will127534/RaspberryPiAtomicNixieClock/PCB/NixieAtomicClock.kicad_sch

## KiCad design PCB/NixieAtomicClock.kicad_sch (2021-09-04)

Schematic: NixieAtomicClock.kicad_sch

Parts:
C1, C3, C7, C12, C33, C56, C66, C89: 100nF; C_0201_0603Metric
C4, C10, C85, C97, C102: CGA5L1X7R1H106K160AC; C_1206_3216Metric
C5: 390pF; C_0201_0603Metric
C6, C8, C9: 680pF; C_0201_0603Metric
C13, C16, C70: 100nF; C_0603_1608Metric
C14, C19, C21, C23, C28, C29, C30, C31, C32, C38, C39, C41, C46, C50, C55, C57, C62, C67, C68, C71, C78, C80, C81, C82, C83, C84, C86, C87, C99: 100nF; C_0402_1005Metric
C17, C27, C47, C48, C100: 1uF; C_0201_0603Metric
C18, C101: 47uF; C_1206_3216Metric
C20, C22: 4.7uF; C_0402_1005Metric
C24, C25, C49, C75, C76, C77, C79: 10uF; C_0402_1005Metric
C26, C43, C51, C53, C61, C74, C98, C104, C105: 1uF; C_0402_1005Metric
C34: 15pF; C_0402_1005Metric
C36, C73: ACH32C-104-T001
C37, C42, C44, C69, C90: GRM188R60J476ME15J; C_0603_1608Metric
C40: CGA5L1X7R1H106K160AC; C_0805_2012Metric
C45: 47uF; C_0805_2012Metric
C52: 10uF; C_0805_2012Metric
C54: EMZR100ARA102MHA0G; CP_Elec_8x10
C58, C59, C60, C63: 56pF; C_0402_1005Metric
C72, C91: 10uF; C_0603_1608Metric
C88, C92, C93, C94: 1uF; C_0603_1608Metric
D1, D2, D3, D4, D5, D6, D7, D8, D10, D12, D14, D17, D18, D19, D20: SMD-LED-CLEAR-BLUE_0603_; LED-0603; MPN 19-217-BHC-ZL1M2RY-3T
D9, D11, D13, D15, D16: D_TVS; D_0402_1005Metric
FAN1, FAN2: M06SMD-1MM; 1X06-1MM
FL2: DLW5ATH500MQ2L; FIL_DLW5ATH500MQ2L; PARTREV N/A
H1, H2, H5, H6, H7, H8: MOUNT-HOLE3.2; 3,2
J1, J2: M06SMD-1MM; 1X06-1MM
J3: M024UCON-15767; JST-2-SMD-VERT
J4, J5: CONN-POWER-JACK-2.1MM_DC-005_; DCJ3P-11.6X9.6X7.0MM; MPN DC-005
J6: 1-1734248-5; TE_1-1734248-5
J7: 47219-2001; MOLEX_47219-2001
J8: QWIIC_CONNECTORJS-1MM; 1X04_1MM_RA
J9, J10, J11: Conn_Coaxial; U.FL_Hirose_U.FL-R-SMT-1_Vertical
J12: USB_C_Receptacle_USB2.0; USB_C_Receptacle_XKB_U262-16XN-4BVC11
J13, J14, J15, J16: Conn_Coaxial; SMA_Samtec_SMA-J-P-X-ST-EM1_EdgeMount
L1, L5: 27nH; L_0402_1005Metric
L2, L3, L4: 1uH; L_0201_0603Metric
L6: FB; L_0201_0603Metric
L7: 4.7uH; L_Vishay_IHLP-2525
L8: L_Coupled_1243; L_CommonModeChoke_Coilcraft_0805USB
L9: 5.6uH; L_Coilcraft_XAL5030
Module1: ComputeModule4-CM4; Raspberry-Pi-4-Compute-Module
Q1, Q2, Q3: BSS214NW; SOT-323_SC-70
R1: 50R; R_0201_0603Metric
R2, R3, R18: 470R; R_0402_1005Metric
R4, R33: 10k; R_0402_1005Metric
R5: 12.4K; R_0402_1005Metric
R6: 2.37K; R_0402_1005Metric
R7, R15, R16: 10m; R_0402_1005Metric
R8: 50R; R_0402_1005Metric
R9, R20, R22, R23, R24, R26, R29, R37, R51, R66, R69, R73, R74: 10K; R_0402_1005Metric
R10: 10.7K; R_0402_1005Metric
R11: 634K; R_0402_1005Metric
R12, R14, R46, R47, R58, R59, R60, R61, R62, R63: 10R; R_0402_1005Metric
R17: 50m; R_0402_1005Metric
R19, R70, R71: 100R; R_0402_1005Metric
R21: 21.5K; R_0402_1005Metric
R25: 470k; R_0402_1005Metric
R27: 900K; R_0402_1005Metric
R28, R30, R31, R32, R34, R35, R53, R54, R55: 4.7K; R_0402_1005Metric
R36: 200K; R_0402_1005Metric
R38, R39, R64, R65: DNP; R_0402_1005Metric
R40: 1K; R_1206_3216Metric
R41, R42: 330R; R_0402_1005Metric
R43, R44, R45, R67, R68: 1K; R_0402_1005Metric
R48, R76: 100K; R_0402_1005Metric
R49: 30R; R_0402_1005Metric
R50: 52.3K; R_0402_1005Metric
R52: R; R_0402_1005Metric
R72: 47K; R_0402_1005Metric
R77: 22.1K; R_0402_1005Metric
TP1, TP2, TP3, TP4, TP5, TP6, TP7, TP8, TP9, TP10, TP11, TP12, TP13, TP14, TP15, TP16, TP17, TP18, TP19, TP20, TP21: TestPoint; TestPoint_Pad_D1.0mm
U1: ICE5LP1K-SG48; QFN-48-1EP_7x7mm_P0.5mm_EP5.6x5.6mm
U2: TPS7A8500ARGRR
U3, U10: TPS7A4700RGWR
U4, U7, U12, U14: INA219AxDCN; SOT-23-8
U5: TDC7200PW
U6: ADS1115IDGS; TSSOP-10_3x3mm_P0.5mm
U9: ADS8681RUM; QFN-16-1EP_4x4mm_P0.65mm_EP2.7x2.7mm
U11: TPS259270DRCR
U13, U28: SN74AUP1G125DSFR
U15: TMP117AIDRVR
U16, U25: D3V3F4U10LP-7; Diodes_UDFN-10_1.0x2.5mm_P0.5mm
U17: LP5912-1.2DRV; WSON-6-1EP_2x2mm_P0.65mm_EP1x1.6mm_ThermalVias
U18: LMK1C1104; LMK1C1102PWR
U19, U30: AD5693RACPZ-RL7
U20: Si5351C-B-GM; QFN-20-1EP_4x4mm_P0.5mm_EP2.7x2.7mm
U21: TPD3S044; SOT-23-6
U22: TUSB320; Texas_X2QFN-12_1.6x1.6mm_P0.4mm
U23: NEO-M8T; ublox_NEO
U24: BGS12P2L6E6327XTSA1
U26: MagJack-A70-112-331N126; TRJG0926HENL
U27: EMC2301; EMC2101-ACZT-TR
U29, U32, U33: TVS2200DRVR
U31: TPS56339DDC; SOT-23-6
U34: LM60440DRPKR
U$9: SA.32M; SA.3X
U$12: NIXIE_POWERSMD; SMD

Connections:
+1V2: C22.2, C47.1, C48.1, R19.1, U1.5 (VCC), U1.30 (VCC), U17.1 (OUT)
+1V8: C66.1, Module1.88 (+1.8v_(Output)), Module1.90 (+1.8v_(Output)), U13.1 (*OE), U13.6 (VCC)
+3.3V: C57.1, R2.2, R3.2, R18.2, R31.2, R33.2, R34.2, R35.2, R36.2, R38.2, R43.2, R44.2, R45.2, R53.2, R54.2, R55.2, R67.2, R68.2, U22.12 (VDD), U26.15 (LEDG_A), U26.17 (LEDY_A)
+3.3VA: C3.2, C7.2, C12.1, C14.1, C19.1, C21.1, C27.2, C28.2, C29.2, C30.2, C31.2, C32.2, C33.1, C45.2, C46.1, C50.2, C56.2, C61.2, C62.2, C77.2, C78.2, C83.1, J8.2 (VCC), L6.1, R24.2, R46.2, R47.2, TP6.1, U1.1 (VCCIO_2), U1.22 (SPI_VCCIO1), U1.24 (VPP_2V5), U1.33 (VCCIO_0), U3.1 (OUT), U3.3 (SENSE_FB), U3.20 (OUT), U4.4 (VS), U4.7 (A0), U4.8 (A1), U5.14 (VDD), U6.8 (VDD), U7.4 (VS), U9.7 (~RST), U9.14 (DVDD), U12.4 (VS), U14.4 (VS), U14.8 (A1), U15.4 (ADD0), U15.5 (V+), U20.10 (VDDOB), U20.11 (VDDOA), U20.14 (VDDOD), U20.18 (VDDOC), U20.20 (VDD), U23.22 (V_BCKP), U23.23 (VCC), U24.4 (VDD), U30.1 (VDD), U30.4 (A0)
+3V3: C20.2, C52.1, C84.1, C89.1, J2.5, J7.4 (VDD), Module1.78 (GPIO_VREF(1.8v/3.3v_Input)), Module1.84 (+3.3v_(Output)), Module1.86 (+3.3v_(Output)), R73.2, U17.4 (EN), U17.6 (IN), U27.3 (VDD), U28.1 (*OE), U28.6 (VCC)
+5V: C53.2, J2.6, Module1.77 (+5v_(Input)), Module1.79 (+5v_(Input)), Module1.81 (+5v_(Input)), Module1.83 (+5v_(Input)), Module1.85 (+5v_(Input)), Module1.87 (+5v_(Input)), R15.2, R32.2, R37.2, R59.2, U21.3 (IN)
+5VA: C41.2, C54.1, C69.2, C70.2, C71.2, C72.2, C76.2, C90.2, C91.2, R5.2, R23.2, R69.2, TP7.1, U2.1 (OUT), U2.19 (OUT), U2.20 (OUT), U19.1 (VDD), U$9.5 (VCC)
+5VL: C18.2, C26.2, R26.2, U9.16 (AVDD), U10.1 (OUT), U10.3 (SENSE_FB), U10.20 (OUT)
ACLoadON: Module1.25 (GPIO21), Q2.1 (G), R29.1
ADC_CONV: U1.19 (IOB_29b), U9.9 (CONVST/~CS)
ADC_MISO: U1.21 (IOB_23b), U9.11 (SDO-0)
ADC_MOSI: U1.18 (IOB_31b), U9.8 (SDI)
ADC_SCLK: U1.20 (IOB_25b_G3), U9.10 (SCLK)
Disable_LED: Module1.29 (GPIO16), Q3.1 (G), R73.1
ETH_LED1: Module1.19 (Ethernet_nLED1(3.3v)), R41.2
ETH_LED2: Module1.17 (Ethernet_nLED2(3.3v)), R42.2
ETH_P0+: Module1.12 (Ethernet_Pair0_P), U16.5, U16.6, U26.1 (TRD0+)
ETH_P0-: Module1.10 (Ethernet_Pair0_N), U16.4, U16.7, U26.2 (TRD0-)
ETH_P1+: Module1.4 (Ethernet_Pair1_P), U16.1, U16.10, U26.3 (TRD1+)
ETH_P1-: Module1.6 (Ethernet_Pair1_N), U16.2, U16.9, U26.6 (TRD1-)
ETH_P2+: Module1.11 (Ethernet_Pair2_P), U25.1, U25.10, U26.7 (TRD2+)
ETH_P2-: Module1.9 (Ethernet_Pair2_N), U25.2, U25.9, U26.8 (TRD2-)
ETH_P3+: Module1.3 (Ethernet_Pair3_P), U25.5, U25.6, U26.9 (TRD3+)
ETH_P3-: Module1.5 (Ethernet_Pair3_N), U25.4, U25.7, U26.10 (TRD3-)
FAN_OUT: FAN1.4, TP19.1, U27.6 (TACH)
FAN_PWM: FAN1.5, TP18.1, U27.5 (PWM)
FPGA_CDONE: D14.2 (-), Module1.50 (GPIO17), U1.7 (CDONE)
FPGA_PPS: Module1.28 (GPIO13), U1.13 (IOB_24a)
FPGA_PPS2: U1.12 (IOB_22b), U13.2 (A)
FPGA_RST: Module1.48 (GPIO27), U1.8 (~CRESET)
FPGA_SCK: Module1.38 (GPIO11), U1.15 (IOB_34a_SPI_SCK)
FPGA_SI: Module1.44 (GPIO10), U1.17 (IOB_33b_SPI_SI)
FPGA_SO: Module1.40 (GPIO9), U1.14 (IOB_32a_SPI_SO)
FPGA_SS: Module1.39 (GPIO8), U1.16 (IOB_35b_SPI_SS)
GND: C3.1, C4.1, C5.1, C6.1, C7.1, C8.1, C9.1, C10.1, C12.2, C13.1, C14.2, C16.1, C17.1, C18.1, C19.2, C20.1, C21.2, C22.1, C23.1, C24.1, C25.1, C26.1, C27.1, C28.1, C29.1, C30.1, C31.1, C32.1, C33.2, C36.2 (GND), C37.1, C38.1, C39.1, C40.1, C42.1, C43.1, C44.1, C45.1, C46.2, C47.2, C48.2, C49.2, C50.1, C51.1, C52.2, C53.1, C54.2, C55.2, C56.1, C57.2, C60.1, C61.1, C62.1, C63.1, C66.2, C68.1, C69.1, C70.1, C71.1, C72.1, C73.2 (GND), C74.1, C75.1, C76.1, C77.1, C78.1, C79.1, C83.2, C84.2, C85.1, C86.1, C88.1, C89.2, C90.1, C91.1, C92.1, C93.1, C94.1, C97.1, C98.1, C100.1, C101.1, C102.1, C104.1, C105.1, D4.2 (-), D7.2 (-), D9.1 (A1), D11.1 (A1), D13.1 (A1), D15.1 (A1), D16.1 (A1), FAN1.1, FAN2.6, FL2.3, J1.1, J2.1, J3.GND (1), J5.2 (-), J6.1, J6.1_1 (1), J6.4, J6.4_1 (4), J6.7, J6.7_1 (7), J6.10, J6.10_1 (10), J6.13, J6.13_1 (13), J7.6 (VSS), J7.G1 (GND@1), J7.G2 (GND@2), J7.G3 (GND@3), J7.G4 (GND@4), J8.1 (GND), J9.2 (Ext), J10.2 (Ext), J11.2 (Ext), J12.A1 (GND), J12.A12 (GND), J12.B1 (GND), J12.B12 (GND), J13.2 (Ext), J14.2 (Ext), J15.2 (Ext), J16.2 (Ext), Module1.1 (GND), Module1.2 (GND), Module1.7 (GND), Module1.8 (GND), Module1.13 (GND), Module1.14 (GND), Module1.22 (GND), Module1.23 (GND), Module1.32 (GND), Module1.33 (GND), Module1.42 (GND), Module1.43 (GND), Module1.52 (GND), Module1.53 (GND), Module1.59 (GND), Module1.60 (GND), Module1.65 (GND), Module1.66 (GND), Module1.71 (GND), Module1.74 (GND), Module1.98 (GND), Module1.107 (GND), Module1.108 (GND), Module1.113 (GND), Module1.114 (GND), Module1.119 (GND), Module1.120 (GND), Module1.125 (GND), Module1.126 (GND), Module1.131 (GND), Module1.132 (GND), Module1.137 (GND), Module1.138 (GND), Module1.144 (GND), Module1.150 (GND), Module1.155 (GND), Module1.156 (GND), Module1.161 (GND), Module1.162 (GND), Module1.167 (GND), Module1.168 (GND), Module1.173 (GND), Module1.174 (GND), Module1.179 (GND), Module1.180 (GND), Module1.185 (GND), Module1.186 (GND), Module1.191 (GND), Module1.192 (GND), Module1.197 (GND), Module1.198 (GND), Q1.2 (S), Q2.2 (S), Q3.2 (S), R6.1, R9.2, R10.1, R22.2, R28.1, R29.2, R30.1, R39.2, R48.2, R51.1, R66.1, R77.1, TP8.1, TP9.1, TP10.1, TP11.1, TP13.1, TP16.1, U1.36 (IOT_48b), U1.49 (GND), U2.8 (GND), U2.18 (GND), U2.21 (PAD), U3.2 (NC), U3.7 (GND), U3.8 (1P6V), U3.11 (0P2V), U3.12 (0P1V), U3.17 (NC), U3.18 (NC), U3.19 (NC), U3.21 (PAD), U4.3 (GND), U5.7 (GND), U6.1 (ADDR), U6.3 (GND), U7.3 (GND), U7.8 (A1), U9.1 (AGND), U9.3 (REFGND), U9.6 (AIN_GND), U9.15 (DGND), U9.17 (PAD), U10.2 (NC), U10.6 (3P2V), U10.7 (GND), U10.10 (0P4V), U10.17 (NC), U10.18 (NC), U10.19 (NC), U10.21 (PAD), U11.11 (EPAD), U12.3 (GND), U12.8 (A1), U13.3 (GND), U14.3 (GND), U14.7 (A0), U15.2 (GND), U16.3 (VSS), U16.8 (VSS), U17.5 (GND), U17.7 (EP), U18.4 (GND), U19.2 (*LDAC), U19.3 (GND), U19.4 (A0), U19.9 (EP), U20.7 (OEB), U20.21 (GND), U21.2 (GND), U22.10 (GND), U22.11 (~EN), U23.7 (VDD_USB), U23.10 (GND), U23.12 (GND), U23.13 (GND), U23.24 (GND), U24.2 (GND), U25.3 (VSS), U25.8 (VSS), U26.19 (SHIELD), U26.20 (SHIELD), U27.4 (GND), U28.3 (GND), U29.1 (GND), U29.2 (GND), U29.3 (GND), U29.7 (PAD), U30.2 (*LDAC), U30.3 (GND), U30.9 (EP), U31.1 (GND), U33.4 (IN), U33.5 (IN), U33.6 (IN), U34.1 (PGND), U34.6 (AGND), U34.11 (PGND), U34.13 (PGND), U$9.2 (GND_SH), U$9.4 (GND), U$12.P$1 (GND), U$12.P$4 (GND)
GPS_ANT_SW: Module1.49 (GPIO18), R66.2, U24.6 (CTRL)
GPS_RX: Module1.55 (GPIO14), R71.2
GPS_TX: Module1.51 (GPIO15), R70.2
HV: J3.VCC (2)
INT_NIXIE: J2.2, Module1.30 (GPIO6), R53.1
IOB_0: FAN2.4, U1.46 (IOB_0a)
IOB_2: FAN2.5, U1.47 (IOB_2a)
IOB_3: FAN2.3, U1.44 (IOB_3b_G6)
IOB_16: Module1.24 (GPIO26), U1.9 (IOB_16a)
IOB_18: Module1.26 (GPIO19), U1.10 (IOB_18a)
IOB_20: Module1.27 (GPIO20), U1.11 (IOB_20a)
IOT_49: FAN2.2, U1.43 (IOT_49a)
IOT_51: FAN2.1, U1.42 (IOT_51a)
ISENSE_5V_P: C40.2, C88.2, C92.2, C93.2, C94.2, FAN1.6, L9.2, R15.1, R20.2, R50.2, R58.2, TP4.1, TP17.1, U3.13 (EN), U3.15 (IN), U3.16 (IN)
ISENSE_MAC_N: C37.2, C38.2, C42.2, C44.2, R4.2, R16.2, R61.2, TP5.1, U2.15 (IN), U2.16 (IN), U2.17 (IN)
ISENSE_MAC_P: C13.2, C16.2, C34.2, C101.2, C102.2, L7.2, R16.1, R60.2, R76.2
ISENSE_NIXIE_N: R17.2, R63.2, U$12.P$2 (IN)
ISENSE_NIXIE_P: C10.2, C36.1, C85.2, C86.2, J6.14, J6.14_1 (14), J6.15, J6.15_1 (15), R7.2, R12.2, R17.1, R62.2, R72.2, TP12.1, U10.13 (EN), U10.15 (IN), U10.16 (IN), U31.3 (VIN)
ISENSE_SYS_N: R7.1, R14.2, U11.6 (OUT), U11.7 (OUT), U11.8 (OUT)
MAC_10MHZ: TP3.1, U1.34 (IOT_44b), U1.35 (IOT_46b_G0), U5.5 (CLOCK), U18.1 (CLKIN), U20.6 (CLKIN), U$9.3 (10MHZ)
MAC_EN: R4.1, U2.14 (EN), U34.8 (PG)
MAC_LOCK: U1.38 (IOT_50b), U$9.6 (BITE)
MAC_RX: Module1.54 (GPIO4), U$9.8 (RX)
MAC_TX: Module1.34 (GPIO5), U$9.7 (TX)
NIXIE_BL: J1.2, R35.1, U1.48 (IOB_4a)
NIXIE_CLK: J1.4, R31.1, U1.3 (IOB_9b)
NIXIE_DIN: J1.6, R28.2, U1.6 (IOB_13b)
NIXIE_LE: J1.5, R30.2, U1.4 (IOB_8a)
NIXIE_POL: J1.3, R34.1, U1.2 (IOB_6a)
unnamed: C1.1, R1.2
unnamed: C1.2, C5.2, L2.1
unnamed: C6.2, L2.2, L3.1
unnamed: C8.2, L3.2, L4.1
unnamed: C9.2, D13.2 (A2), J14.1 (In), L4.2
unnamed: C17.2, U10.14 (NR)
unnamed: C23.2, U9.2 (REFIO)
unnamed: C24.2, U19.7 (VREF)
unnamed: C25.2, C79.2, U9.4 (REFCAP)
unnamed: C34.1, R76.1, R77.2, U34.7 (FB)
unnamed: C39.2, U2.13 (NR_SS)
unnamed: C41.1, R5.1, R6.2, U2.3 (FB)
unnamed: C43.2, U3.14 (NR)
unnamed: C49.1, R19.2, U1.29 (VCCPLL)
unnamed: C51.2, U5.13 (VREG)
unnamed: C55.1, U26.4 (CT), U26.5 (CT)
unnamed: C58.1, D16.2 (A2), J11.1 (In), L5.2
unnamed: C58.2, U24.1 (RF2)
unnamed: C59.1, D15.2 (A2), J15.1 (In), L1.2
unnamed: C59.2, U24.3 (RF1)
unnamed: C60.2, L1.1, R46.1
unnamed: C63.2, L5.1, R47.1
unnamed: C67.1, R14.1, U7.2 (IN-)
unnamed: C67.2, R12.1, U7.1 (IN+)
unnamed: C68.2, R21.1, R22.1, U9.5 (AIN_P)
unnamed: C73.1, FL2.2
unnamed: C73.3 (2), U11.2 (EN/UVLO), U11.3 (VIN), U11.4 (VIN), U11.5 (VIN)
unnamed: C74.2, U11.1 (DV/DT)
unnamed: C75.2, U30.7 (VREF)
unnamed: C80.1, R59.1, U12.2 (IN-)
unnamed: C80.2, R58.1, U12.1 (IN+)
unnamed: C81.1, R61.1, U14.2 (IN-)
unnamed: C81.2, R60.1, U14.1 (IN+)
unnamed: C82.1, R63.1, U4.2 (IN-)
unnamed: C82.2, R62.1, U4.1 (IN+)
unnamed: C87.1, L9.1, U31.2 (SW)
unnamed: C87.2, R49.1
unnamed: C98.2, U34.5 (VCC)
unnamed: C99.1, U34.3 (NC)
unnamed: C99.2, U34.4 (BOOT)
unnamed: C100.2, L6.2, U18.2 (1G), U18.6 (VDD)
unnamed: C4.2, C36.3 (2), C97.2, C104.2, C105.2, U34.2 (VIN), U34.9 (EN), U34.10 (VIN)
unnamed: D1.1 (+), R2.1
unnamed: D1.2 (-), U1.41 (RGB2)
unnamed: D2.1 (+), R3.1
unnamed: D2.2 (-), U1.40 (RGB1)
unnamed: D3.1 (+), R18.1
unnamed: D3.2 (-), U1.39 (RGB0)
unnamed: D4.1 (+), R23.1
unnamed: D5.1 (+), R24.1
unnamed: D6.1 (+), R20.1
unnamed: D7.1 (+), R25.1
unnamed: D8.1 (+), R26.1
unnamed: D9.2 (A2), R10.2, R11.1, U6.4 (AIN0)
unnamed: D10.1 (+), R43.1
unnamed: D11.2 (A2), J13.1 (In), R8.2
unnamed: D12.1 (+), R44.1
unnamed: D12.2 (-), U28.4 (*Y)
unnamed: D14.1 (+), R45.1
unnamed: D17.1 (+), R32.1
unnamed: D18.1 (+), R33.1
unnamed: D19.1 (+), R69.1
unnamed: D19.2 (-), U2.4 (PG)
unnamed: D20.1 (+), R72.1
unnamed: D5.2 (-), D6.2 (-), D8.2 (-), D20.2 (-), Q3.3 (D)
unnamed: FL2.1, J4.1 (+), U29.4 (IN), U29.5 (IN), U29.6 (IN)
unnamed: FL2.4, J4.2 (-)
unnamed: J5.1 (+), R21.2, R40.1, U32.4 (IN), U32.5 (IN), U32.6 (IN)
unnamed: J6.2, J6.2_1 (2), Module1.110 (PCIe_CLK_P)
unnamed: J6.3, J6.3_1 (3), Module1.112 (PCIe_CLK_N)
unnamed: J6.5, J6.5_1 (5), Module1.116 (PCIe_RX_P)
unnamed: J6.6, J6.6_1 (6), Module1.118 (PCIe_RX_N)
unnamed: J6.8, J6.8_1 (8), Module1.122 (PCIe_TX_P)
unnamed: J6.9, J6.9_1 (9), Module1.124 (PCIe_TX_N)
unnamed: J6.11, J6.11_1 (11), Module1.102 (PCIe_CLK_nREQ)
unnamed: J6.12, J6.12_1 (12), Module1.109 (PCIe_nRST)
unnamed: J9.1 (In), U20.9 (CLK2)
unnamed: J12.A4 (VBUS), J12.A9 (VBUS), J12.B4 (VBUS), J12.B9 (VBUS), R27.1, U21.4 (OUT)
unnamed: J12.A5 (CC1), U22.1 (CC1)
unnamed: J12.A6 (D+), J12.B6 (D+), L8.1
unnamed: J12.A7 (D-), J12.B7 (D-), L8.4
unnamed: J12.B5 (CC2), U22.2 (CC2)
unnamed: J16.1 (In), U20.19 (CLK4)
unnamed: L7.1, U34.12 (SW)
unnamed: Module1.16 (Ethernet_SYNC_IN(1.8v)), U13.4 (*Y)
unnamed: Module1.80 (SCL0), R64.1
unnamed: Module1.82 (SDA0), R65.1
unnamed: Q2.3 (D), R40.2
unnamed: R1.1, U18.7 (NC)
unnamed: R8.1, U18.8 (Y1)
unnamed: R27.2, U22.4 (VBUS_DET)
unnamed: R38.1, R39.1, U22.3 (PORT)
unnamed: R41.1, U26.16 (LEDG_K)
unnamed: R42.1, U26.18 (LEDY_K)
unnamed: R48.1, U11.10 (ILIM)
unnamed: R49.2, U31.6 (BOOT)
unnamed: R50.1, R51.2, U31.4 (FB)
unnamed: R52.1, U30.8 (VOUT)
unnamed: R52.2, TP1.1
unnamed: R70.1, U23.20 (TXD/SPI_MISO)
unnamed: R71.1, U23.21 (RXD/SPI_MOSI)
unnamed: R74.2, U23.3 (TIMEPULSE)
unnamed: U23.11 (RF_IN), U24.5 (RFIN)
unnamed: U32.1 (GND), U32.2 (GND), U32.3 (GND), U32.7 (PAD), U33.1 (GND), U33.2 (GND), U33.3 (GND), U33.7 (PAD)
unnamed: U19.8 (VOUT), U$9.1 (VCONT)
RPI_ACT_LED: D10.2 (-), Module1.21 (PI_nLED_Activity)
RPI_PWR_LED: Module1.95 (nPI_LED_PWR), U28.2 (A)
SCL_Board: FAN1.3, J8.4 (SCL), Module1.47 (GPIO23), R64.2, R68.1, TP20.1, U4.5 (SCL), U6.10 (SCL), U7.5 (SCL), U7.7 (A0), U12.5 (SCL), U14.5 (SCL), U15.1 (SCL), U19.5 (SCL), U20.4 (SCL), U27.2 (SCL), U30.5 (SCL)
SCL_NIXIE: J2.4, Module1.56 (GPIO3), R55.1, TP15.1
SDA_Board: FAN1.2, J8.3 (SDA), Module1.46 (GPIO22), R65.2, R67.1, TP21.1, U4.6 (SDA), U6.9 (SDA), U7.6 (SDA), U12.6 (SDA), U12.7 (A0), U14.6 (SDA), U15.6 (SDA), U19.6 (SDA), U20.5 (SDA), U27.1 (SDA), U30.6 (SDA)
SDA_NIXIE: J2.3, Module1.58 (GPIO2), R54.1, TP14.1
SD_CLK: J7.5 (CLK), Module1.57 (SD_CLK)
SD_CMD: J7.3 (CMD), Module1.62 (SD_CMD)
SD_DAT0: J7.7 (DAT0), Module1.63 (SD_DAT0)
SD_DAT1: J7.8 (DAT1), Module1.67 (SD_DAT1)
SD_DAT2: J7.1 (DAT2), Module1.69 (SD_DAT2)
SD_DAT3: J7.2 (CD/DAT3), Module1.61 (SD_DAT3)
TDC_CS: U1.25 (IOT_36b), U5.11 (CS_N)
TDC_EN: R9.1, U1.37 (IOT_45a_G1), U5.1 (ENABLE)
TDC_INT: U1.28 (IOT_41a), U5.8 (INT_N)
TDC_MISO: U1.27 (IOT_38b), U5.9 (DOUT)
TDC_MOSI: U1.26 (IOT_39a), U5.10 (DIN)
TDC_SCLK: U1.23 (IOT_37a), U5.12 (SCLK)
TDC_START: J10.1 (In), R74.1, U1.32 (IOT_43a), U5.3 (START)
TDC_STOP: U1.31 (IOT_42b), U5.4 (STOP)
TDC_TRIG: U1.45 (IOB_5b), U5.2 (TRIGG)
USB_DN: L8.3, Module1.103 (USB2_N), U21.6 (D2)
USB_DP: L8.2, Module1.105 (USB2_P), U21.5 (D1)
USB_ID: D18.2 (-), Module1.101 (USB_OTG_ID), Q1.1 (G), R36.1, U22.9 (ID)
USB_PW_EN: D17.2 (-), Q1.3 (D), R37.1, U21.1 (EN)
VPP: R11.2, R25.2, TP2.1, U$12.P$3 (HV)

Notes on the sheet:
FPGA
Input Power
Power Sensor
Atomic Clock Power
Clock Gen
Connector
TDC7200
Other Power
AC Measurement
Atomic Clock
ETH
GPS
LEDs
USB-C
RASPBERRY PI
MISC
