will127534/RaspberryPiAtomicNixieClock/RPI_Code/autoBrightness/TSL2561.cpp

/**************************************************************************/
/*! 
    @file     tsl2561.c
    @author   K. Townsend (microBuilder.eu / adafruit.com)

    @section LICENSE

    Software License Agreement (BSD License)

    Copyright (c) 2010, microBuilder SARL, Adafruit Industries
    All rights reserved.

    Redistribution and use in source and binary forms, with or without
    modification, are permitted provided that the following conditions are met:
    1. Redistributions of source code must retain the above copyright
    notice, this list of conditions and the following disclaimer.
    2. Redistributions in binary form must reproduce the above copyright
    notice, this list of conditions and the following disclaimer in the
    documentation and/or other materials provided with the distribution.
    3. Neither the name of the copyright holders nor the
    names of its contributors may be used to endorse or promote products
    derived from this software without specific prior written permission.

    THIS SOFTWARE IS PROVIDED BY THE COPYRIGHT HOLDERS ''AS IS'' AND ANY
    EXPRESS OR IMPLIED WARRANTIES, INCLUDING, BUT NOT LIMITED TO, THE IMPLIED
    WARRANTIES OF MERCHANTABILITY AND FITNESS FOR A PARTICULAR PURPOSE ARE
    DISCLAIMED. IN NO EVENT SHALL THE COPYRIGHT HOLDER BE LIABLE FOR ANY
    DIRECT, INDIRECT, INCIDENTAL, SPECIAL, EXEMPLARY, OR CONSEQUENTIAL DAMAGES
    (INCLUDING, BUT NOT LIMITED TO, PROCUREMENT OF SUBSTITUTE GOODS OR SERVICES;
    LOSS OF USE, DATA, OR PROFITS; OR BUSINESS INTERRUPTION) HOWEVER CAUSED AND
    ON ANY THEORY OF LIABILITY, WHETHER IN CONTRACT, STRICT LIABILITY, OR TORT
    (INCLUDING NEGLIGENCE OR OTHERWISE) ARISING IN ANY WAY OUT OF THE USE OF THIS
    SOFTWARE, EVEN IF ADVISED OF THE POSSIBILITY OF SUCH DAMAGE.
*/
/**************************************************************************/

#include <stdlib.h>
#include <wiringPiI2C.h>
#include "TSL2561.h"
#include <stdint.h>
#include <unistd.h>
#include <iostream>
using namespace std;

TSL2561::TSL2561() {
  _initialized = false;
  _integration = TSL2561_INTEGRATIONTIME_13MS;
  _gain = TSL2561_GAIN_16X;
  // we cant do wire initialization till later, because we havent loaded Wire yet
}

bool TSL2561::begin(int fd) {
  _fd = fd;
  _fd = wiringPiI2CSetup(TSL2561_ADDR_LOW);
  uint8_t x = wiringPiI2CReadReg8(fd,TSL2561_REGISTER_ID);
  //Serial.print("0x"); Serial.println(x, HEX);
  if (x & 0x0A ) {
    cout << "Found TSL2561" << endl;
   } else {
    cout << "TSL2561 Not Found" << endl;
    while(1){
    }
   }

  _initialized = true;

  // Set default integration time and gain
  setTiming(_integration);
  setGain(_gain);
  // Note: by default, the device is in power down mode on bootup
  disable();

  return true;
}

void TSL2561::enable(void)
{
  if (!_initialized) begin(_fd);

  // Enable the device by setting the control bit to 0x03
  write8(TSL2561_COMMAND_BIT | TSL2561_REGISTER_CONTROL, TSL2561_CONTROL_POWERON);
}

void TSL2561::disable(void)
{
  if (!_initialized) begin(_fd);

  // Disable the device by setting the control bit to 0x03
  write8(TSL2561_COMMAND_BIT | TSL2561_REGISTER_CONTROL, TSL2561_CONTROL_POWEROFF);
}


void TSL2561::setGain(tsl2561Gain_t gain) {
  if (!_initialized) begin(_fd);

  enable();
  _gain = gain;
  write8(TSL2561_COMMAND_BIT | TSL2561_REGISTER_TIMING, _integration | _gain);  
  disable();
}

void TSL2561::setTiming(tsl2561IntegrationTime_t integration)
{
  if (!_initialized) begin(_fd);

  enable();
  _integration = integration;
  write8(TSL2561_COMMAND_BIT | TSL2561_REGISTER_TIMING, _integration | _gain);  
  disable();
}

uint32_t TSL2561::calculateLux(uint16_t ch0, uint16_t ch1)
{
  unsigned long chScale;
  unsigned long channel1;
  unsigned long channel0;

  switch (_integration)
  {
    case TSL2561_INTEGRATIONTIME_13MS:
      chScale = TSL2561_LUX_CHSCALE_TINT0;
      break;
    case TSL2561_INTEGRATIONTIME_101MS:
      chScale = TSL2561_LUX_CHSCALE_TINT1;
      break;
    default: // No scaling ... integration time = 402ms
      chScale = (1 << TSL2561_LUX_CHSCALE);
      break;
  }

  // Scale for gain (1x or 16x)
  if (!_gain) chScale = chScale << 4;

  // scale the channel values
  channel0 = (ch0 * chScale) >> TSL2561_LUX_CHSCALE;
  channel1 = (ch1 * chScale) >> TSL2561_LUX_CHSCALE;

  // find the ratio of the channel values (Channel1/Channel0)
  unsigned long ratio1 = 0;
  if (channel0 != 0) ratio1 = (channel1 << (TSL2561_LUX_RATIOSCALE+1)) / channel0;

  // round the ratio value
  unsigned long ratio = (ratio1 + 1) >> 1;

  unsigned int b, m;

#ifdef TSL2561_PACKAGE_CS
  if ((ratio >= 0) && (ratio <= TSL2561_LUX_K1C))
    {b=TSL2561_LUX_B1C; m=TSL2561_LUX_M1C;}
  else if (ratio <= TSL2561_LUX_K2C)
    {b=TSL2561_LUX_B2C; m=TSL2561_LUX_M2C;}
  else if (ratio <= TSL2561_LUX_K3C)
    {b=TSL2561_LUX_B3C; m=TSL2561_LUX_M3C;}
  else if (ratio <= TSL2561_LUX_K4C)
    {b=TSL2561_LUX_B4C; m=TSL2561_LUX_M4C;}
  else if (ratio <= TSL2561_LUX_K5C)
    {b=TSL2561_LUX_B5C; m=TSL2561_LUX_M5C;}
  else if (ratio <= TSL2561_LUX_K6C)
    {b=TSL2561_LUX_B6C; m=TSL2561_LUX_M6C;}
  else if (ratio <= TSL2561_LUX_K7C)
    {b=TSL2561_LUX_B7C; m=TSL2561_LUX_M7C;}
  else if (ratio > TSL2561_LUX_K8C)
    {b=TSL2561_LUX_B8C; m=TSL2561_LUX_M8C;}
#else
  if ((ratio >= 0) && (ratio <= TSL2561_LUX_K1T))
    {b=TSL2561_LUX_B1T; m=TSL2561_LUX_M1T;}
  else if (ratio <= TSL2561_LUX_K2T)
    {b=TSL2561_LUX_B2T; m=TSL2561_LUX_M2T;}
  else if (ratio <= TSL2561_LUX_K3T)
    {b=TSL2561_LUX_B3T; m=TSL2561_LUX_M3T;}
  else if (ratio <= TSL2561_LUX_K4T)
    {b=TSL2561_LUX_B4T; m=TSL2561_LUX_M4T;}
  else if (ratio <= TSL2561_LUX_K5T)
    {b=TSL2561_LUX_B5T; m=TSL2561_LUX_M5T;}
  else if (ratio <= TSL2561_LUX_K6T)
    {b=TSL2561_LUX_B6T; m=TSL2561_LUX_M6T;}
  else if (ratio <= TSL2561_LUX_K7T)
    {b=TSL2561_LUX_B7T; m=TSL2561_LUX_M7T;}
  else if (ratio > TSL2561_LUX_K8T)
    {b=TSL2561_LUX_B8T; m=TSL2561_LUX_M8T;}
#endif

  unsigned long temp;
  temp = ((channel0 * b) - (channel1 * m));

  // do not allow negative lux value
  if (temp < 0) temp = 0;

  // round lsb (2^(LUX_SCALE-1))
  temp += (1 << (TSL2561_LUX_LUXSCALE-1));

  // strip off fractional portion
  uint32_t lux = temp >> TSL2561_LUX_LUXSCALE;

  // Signal I2C had no errors
  return lux;
}

uint32_t TSL2561::getFullLuminosity (void)
{
  if (!_initialized) begin(_fd);

  // Enable the device by setting the control bit to 0x03
  enable();

  // Wait x ms for ADC to complete
  switch (_integration)
  {
    case TSL2561_INTEGRATIONTIME_13MS:
      usleep(14000);
      break;
    case TSL2561_INTEGRATIONTIME_101MS:
      usleep(102000);
      break;
    default:
      usleep(403000);
      break;
  }

  uint32_t x;
  x = read16(TSL2561_COMMAND_BIT | TSL2561_WORD_BIT | TSL2561_REGISTER_CHAN1_LOW);
  x <<= 16;
  x |= read16(TSL2561_COMMAND_BIT | TSL2561_WORD_BIT | TSL2561_REGISTER_CHAN0_LOW);

  disable();

  return x;
}
uint16_t TSL2561::getLuminosity (uint8_t channel) {

  uint32_t x = getFullLuminosity();

  if (channel == 0) {
    // Reads two byte value from channel 0 (visible + infrared)
    return (x & 0xFFFF);
  } else if (channel == 1) {
    // Reads two byte value from channel 1 (infrared)
    return (x >> 16);
  } else if (channel == 2) {
    // Reads all and subtracts out just the visible!
    return ( (x & 0xFFFF) - (x >> 16));
  }
  
  // unknown channel!
  return 0;
}


uint16_t TSL2561::read16(uint8_t reg)
{
  return wiringPiI2CReadReg16(_fd,reg);
}



void TSL2561::write8 (uint8_t reg, uint8_t value)
{
  wiringPiI2CWriteReg8(_fd,reg,value);
}
